codecooker1/keeby/PCB/3dout/keeby.png

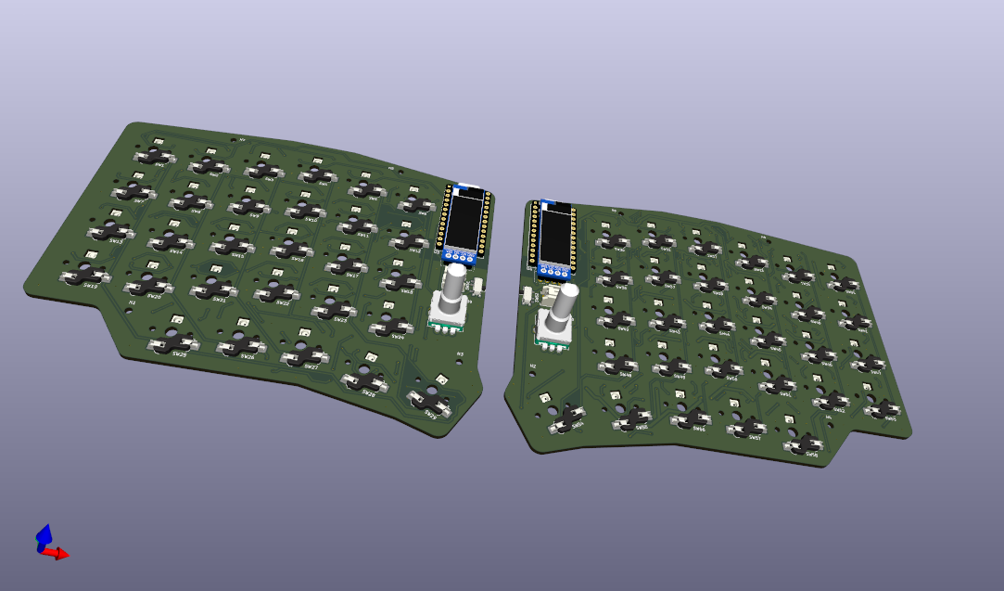
PCB/3dout/keeby.png
